lzxindustries/lzxcadet/C1/Frontpanel/LZX-C1-FPN-V1.0.bmp

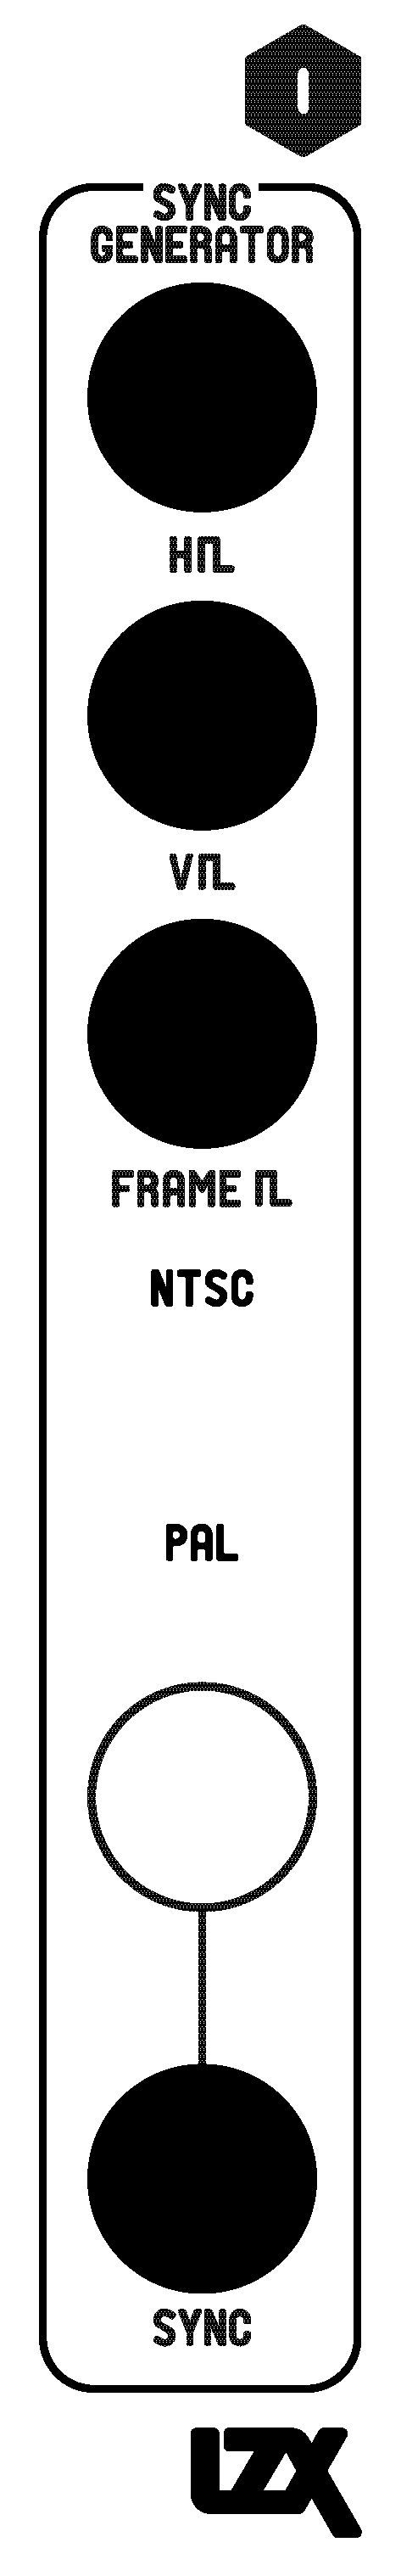
C1/Frontpanel/LZX-C1-FPN-V1.0.bmp
