lzxindustries/lzxcadet/C1/Images/LZX-Industries-Cadet-I-Sync-Generator-Color-Illustration_1024X1024.jpg

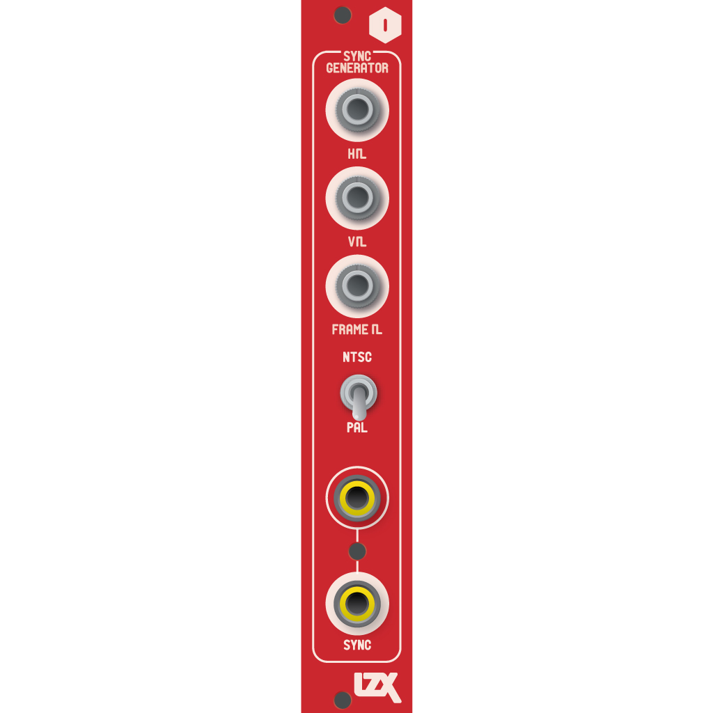
C1/Images/LZX-Industries-Cadet-I-Sync-Generator-Color-Illustration_1024X1024.jpg
