lzxindustries/lzxcadet/C2/Frontpanel/LZX-C2-FPN-V1.0.bmp

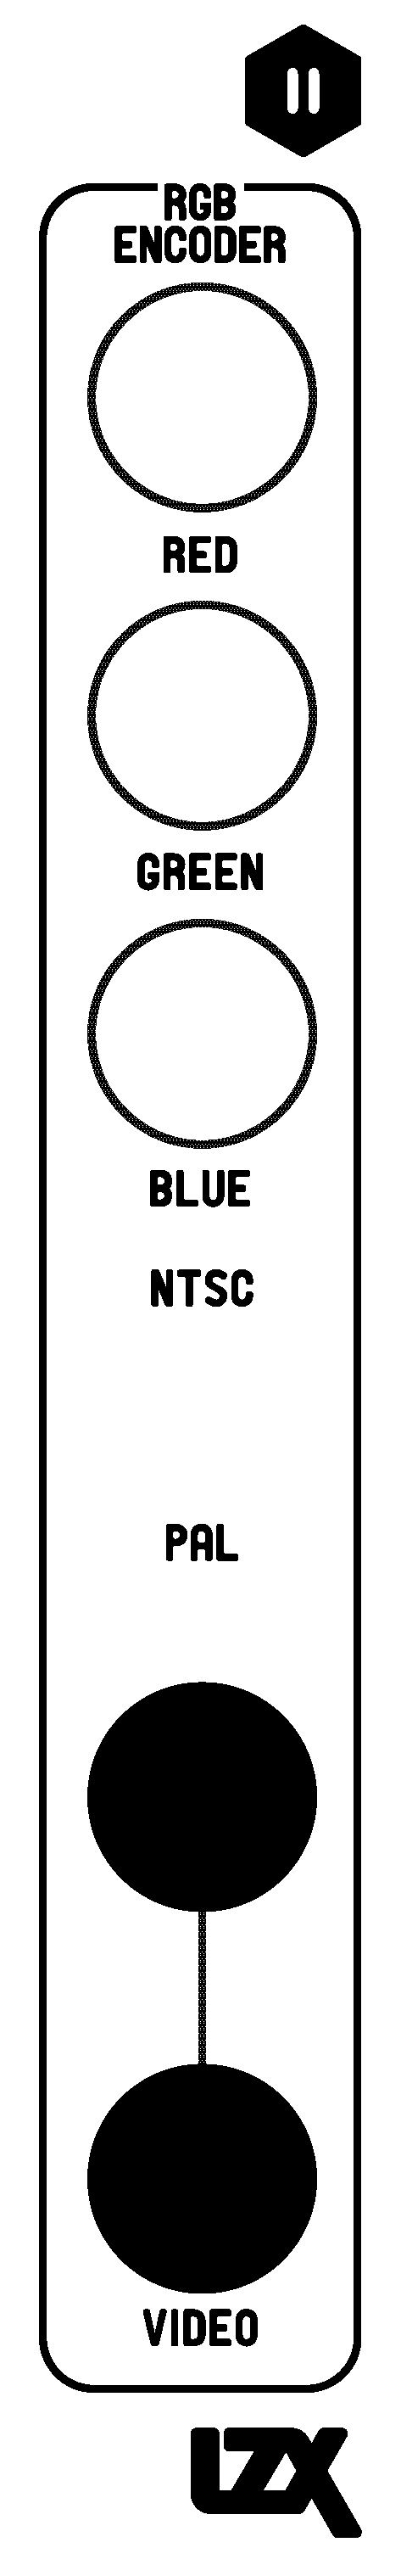
C2/Frontpanel/LZX-C2-FPN-V1.0.bmp
