lzxindustries/lzxcadet/C2/Images/LZX-Industries-Cadet-II-RGB-Encoder-Front-Photo.png

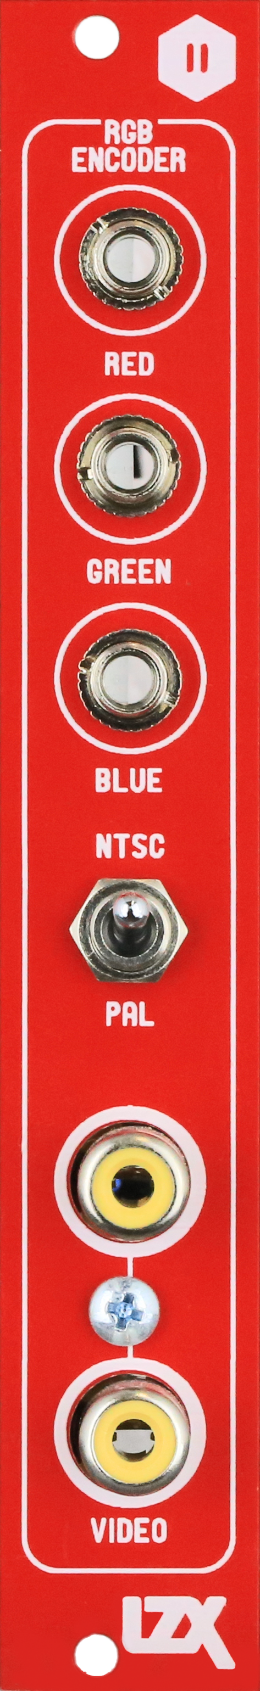
C2/Images/LZX-Industries-Cadet-II-RGB-Encoder-Front-Photo.png
