lzxindustries/lzxcadet/C3/Frontpanel/LZX-C3-FPN-V1.0.bmp

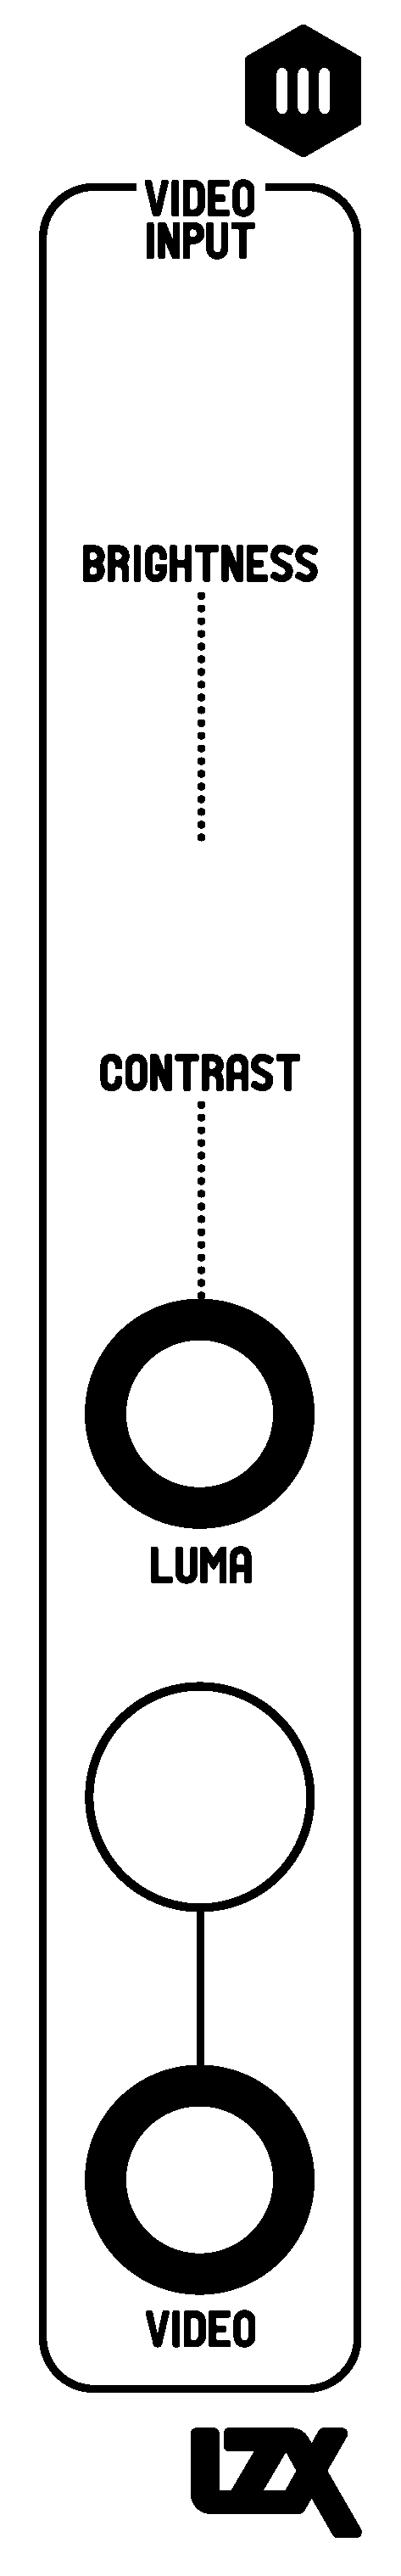
C3/Frontpanel/LZX-C3-FPN-V1.0.bmp
