lzxindustries/lzxcadet/C4/Frontpanel/LZX-C4-FPN-V1.0.bmp

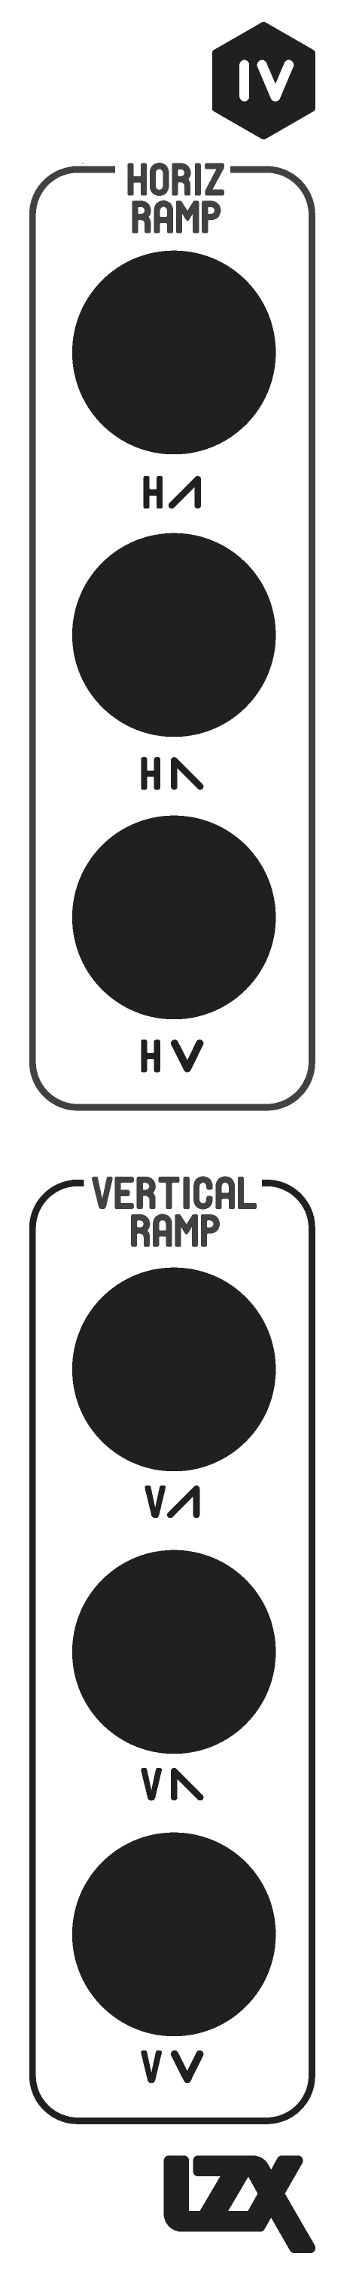
C4/Frontpanel/LZX-C4-FPN-V1.0.bmp
