lzxindustries/lzxcadet/C4/Images/LZX Industries Cadet IV Ramp Generator Front Photo.png

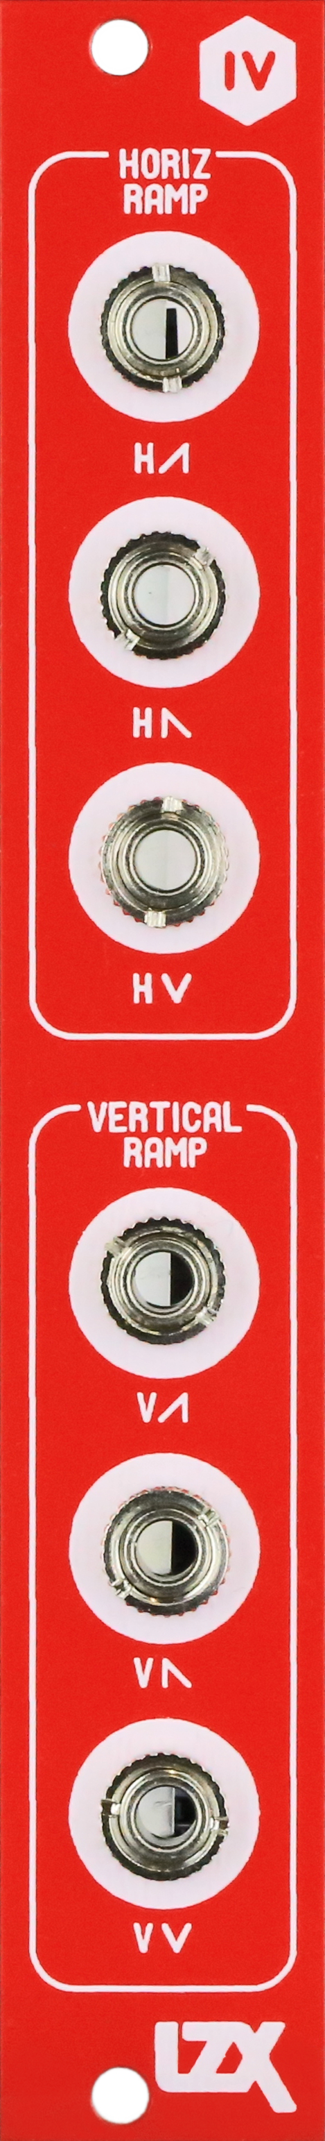
C4/Images/LZX Industries Cadet IV Ramp Generator Front Photo.png
