lzxindustries/lzxcadet/C5/Frontpanel/LZX-C5-FPN-V1.0.bmp

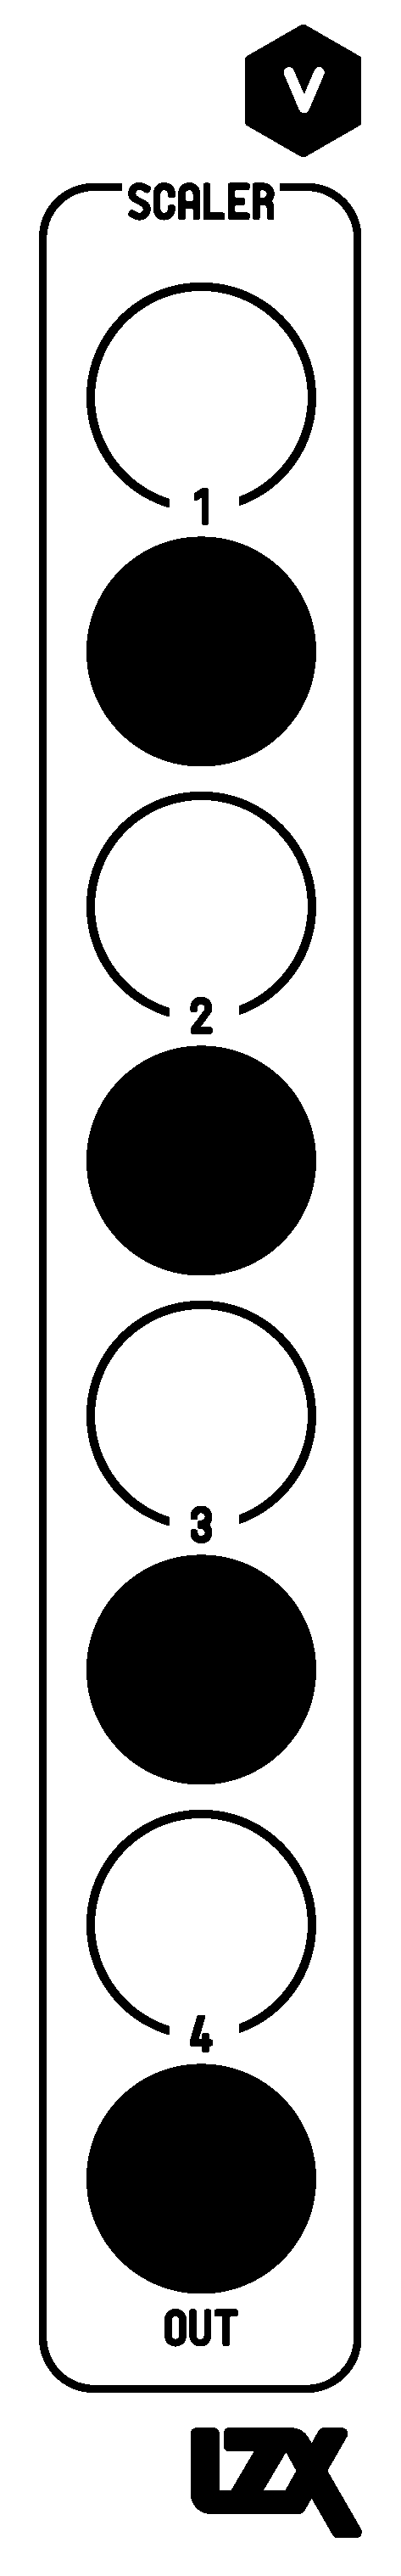
C5/Frontpanel/LZX-C5-FPN-V1.0.bmp
