lzxindustries/lzxcadet/C6/Frontpanel/LZX-C6-FPN-V1.0.bmp

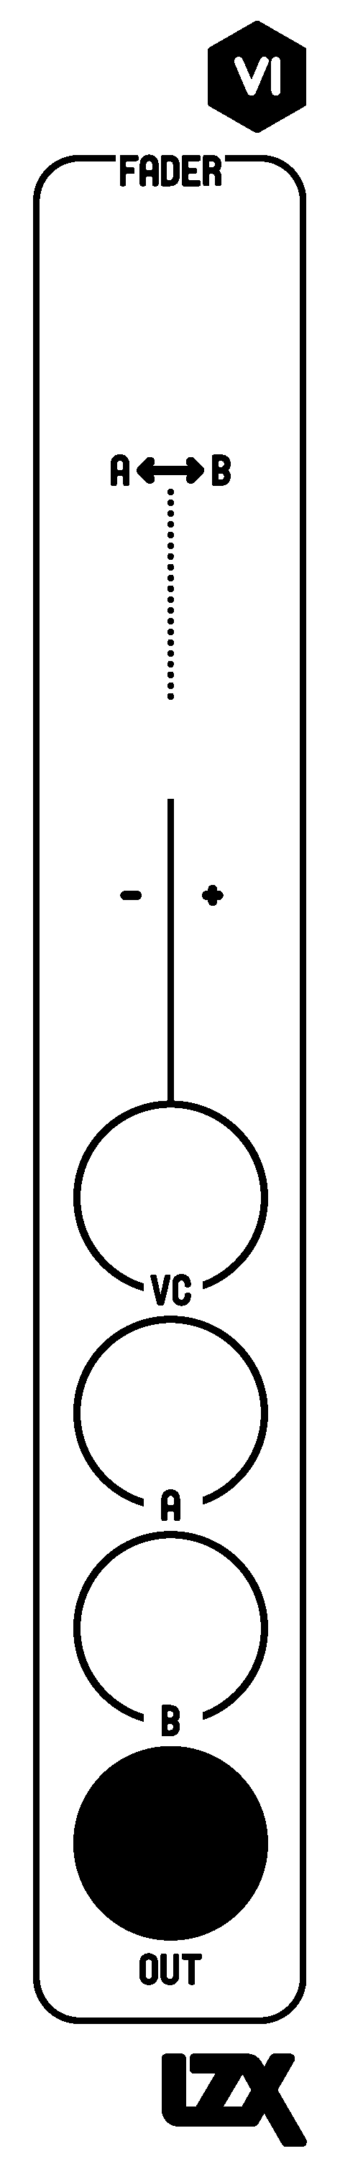
C6/Frontpanel/LZX-C6-FPN-V1.0.bmp
