lzxindustries/lzxcadet/C7/Images/LZX Industries Cadet VII Processor Front Photo.png

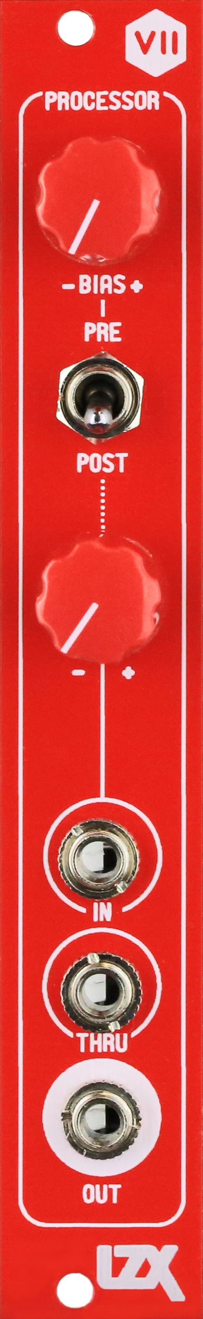
C7/Images/LZX Industries Cadet VII Processor Front Photo.png
