lzxindustries/lzxcadet/C8/Images/LZX Industries Cadet VIII Hard Key Generator Front Photo.png

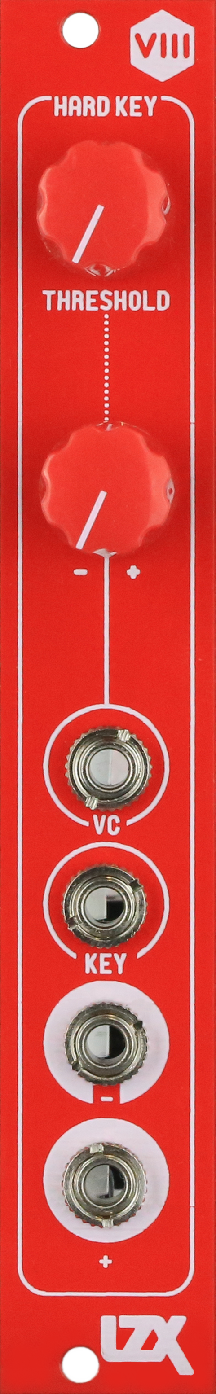
C8/Images/LZX Industries Cadet VIII Hard Key Generator Front Photo.png
