lzxindustries/lzxcadet/C9/Frontpanel/LZX-C9-FPN-V1.0.bmp

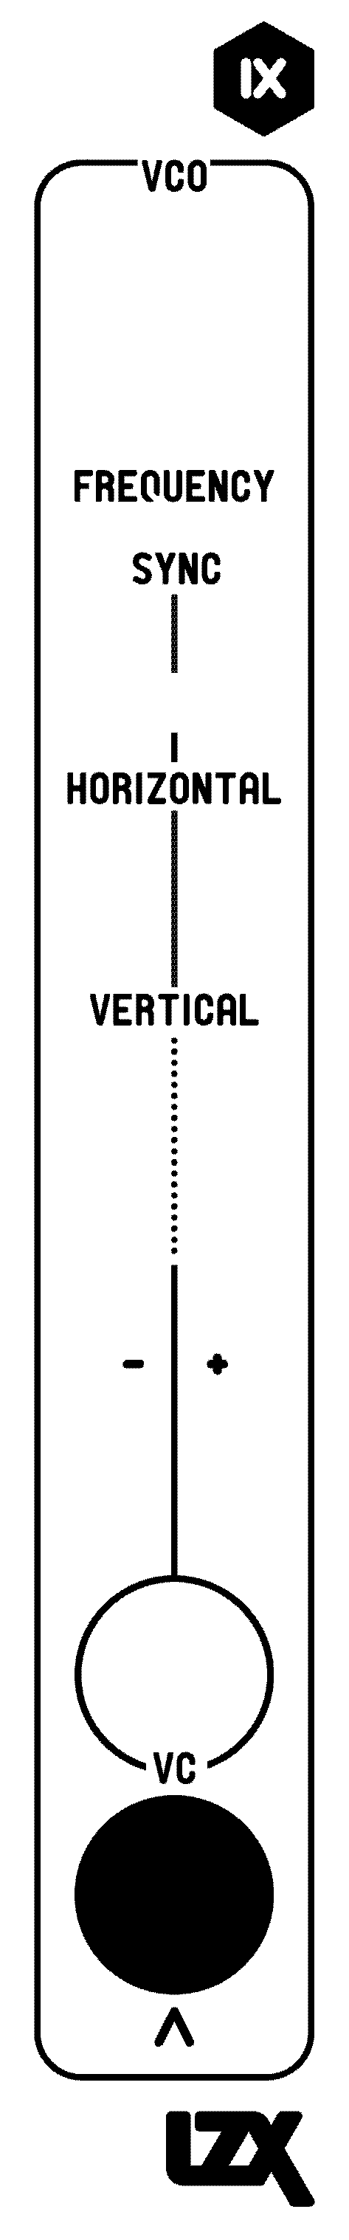
C9/Frontpanel/LZX-C9-FPN-V1.0.bmp
