lzxindustries/lzxcadet/C9/Images/LZX Industries Cadet IX VCO Front Photo.png

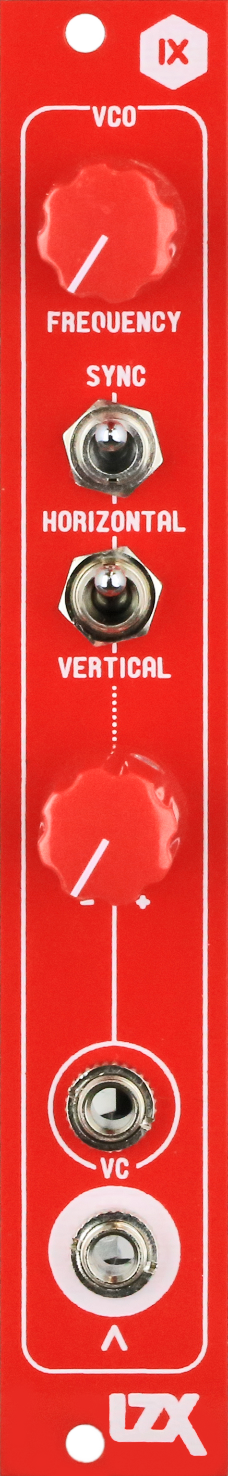
C9/Images/LZX Industries Cadet IX VCO Front Photo.png
