lzxindustries/lzxcadet/C10/Frontpanel/LZX-C10-FPN-V1.0.bmp

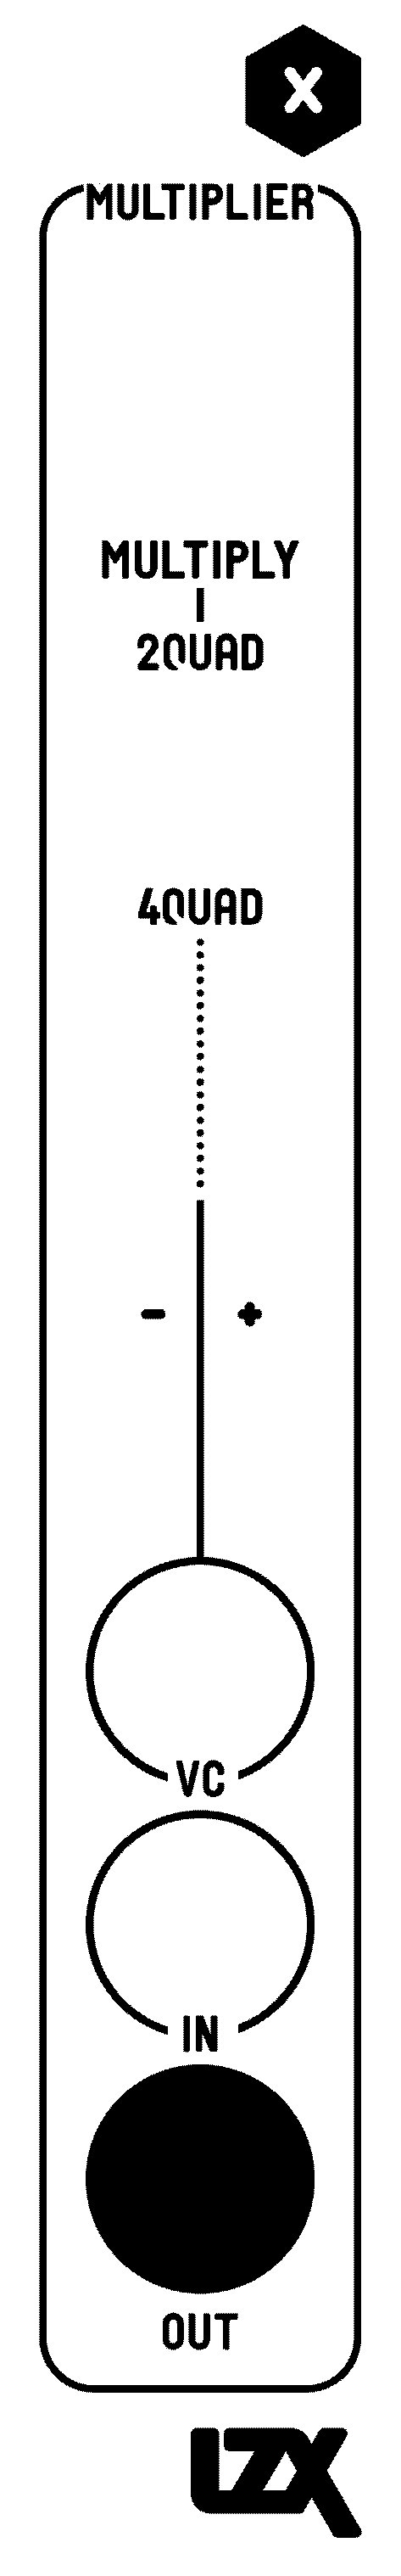
C10/Frontpanel/LZX-C10-FPN-V1.0.bmp
